sondre99v/TinySynth/Software/TinySynth/TinySynth/Modules/module_utils.h

/*
 * module_utils.h
 *
 * Created: 27/08/19 15:26:05
 *  Author: Sondre
 */ 


#ifndef MODULE_UTILS_H_
#define MODULE_UTILS_H_

typedef struct {
	uint8_t base_value;
	uint8_t* mod_source;
	int8_t mod_amount;
} modulated_uint8_t;



#endif /* MODULE_UTILS_H_ */
